MisterGoodDeal/custom-streamdeck/Front face/final_face.dxf

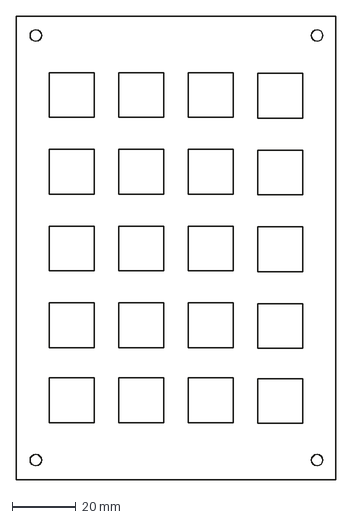
[picture p9: CAD file, 2021-04-16]
Front face/final_face.dxf
100.0 x 145.0 mm
