MisterGoodDeal/custom-streamdeck/Tests/Test Face v1.stl

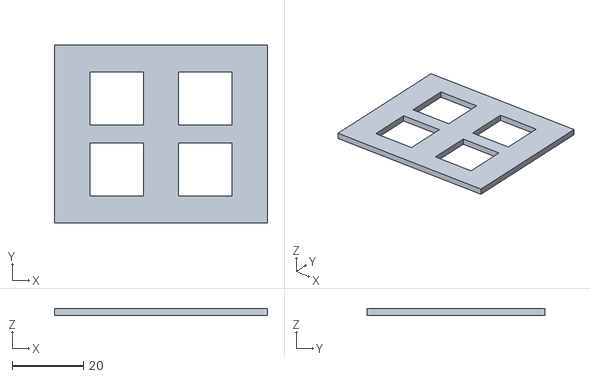
[picture p10: CAD file, 2021-04-16]
Tests/Test Face v1.stl
60.0 x 50.0 x 2.00
