MisterGoodDeal/custom-streamdeck/Body/body_v3.dxf

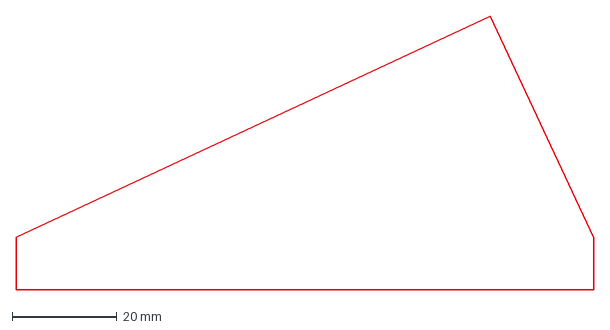
[picture p11: CAD file, 2021-04-16]
Body/body_v3.dxf
110.2 x 52.2 mm
