MisterGoodDeal/custom-streamdeck/Custom keycaps/stemKey.stl

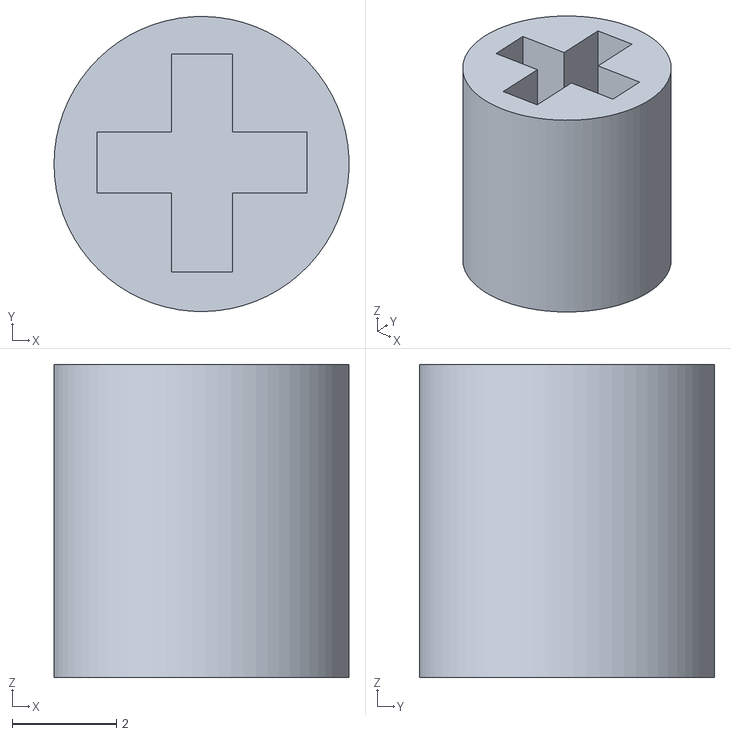
[picture p12: CAD file, 2021-04-16]
Custom keycaps/stemKey.stl
5.65 x 5.65 x 6.00
