MisterGoodDeal/custom-streamdeck/Tests/custom_streamdeck_14mm_test v1.stl

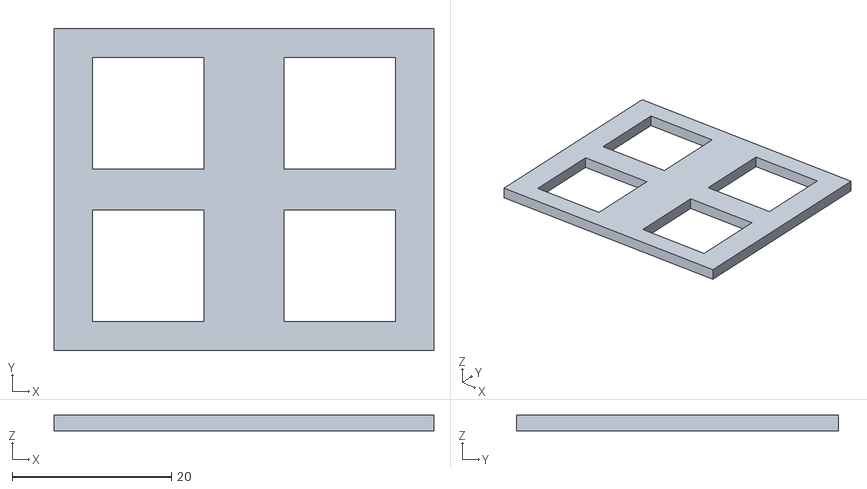
[picture p13: CAD file, 2021-04-16]
Tests/custom_streamdeck_14mm_test v1.stl
47.7 x 40.4 x 2.00
