MisterGoodDeal/custom-streamdeck/Tests/test_face.dxf

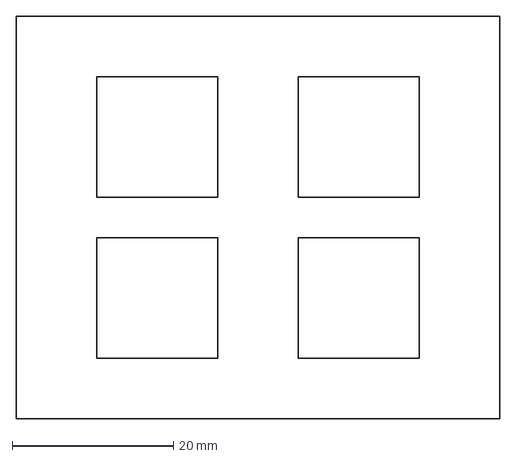
[picture p14: CAD file, 2021-04-16]
Tests/test_face.dxf
60.0 x 50.0 mm
